remne/p1ib/images/case1.jpg

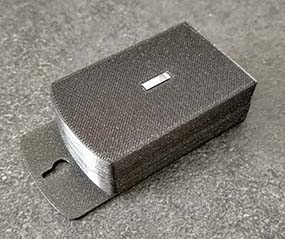
images/case1.jpg
