remne/p1ib/images/case_red.jpg

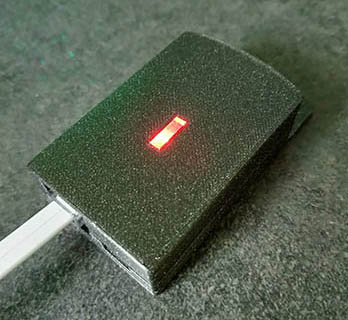
images/case_red.jpg
