remne/p1ib/images/case_rend.png

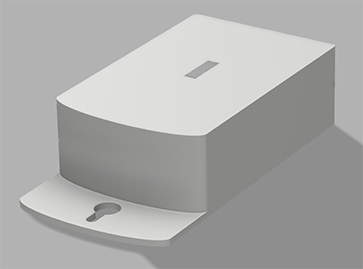
images/case_rend.png
