remne/p1ib/images/hw.jpg

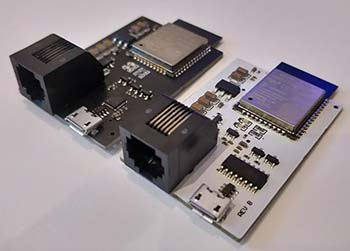
images/hw.jpg
