remne/p1ib/images/ledthingy.jpg

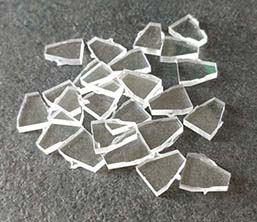
images/ledthingy.jpg
