remne/p1ib/images/settings_power_meter_modes.jpg

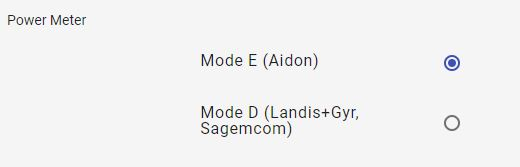
images/settings_power_meter_modes.jpg
